nilsrenner/Selfe-Tuned-Filter/005_Dokumentation/003_Thesis/Theorie/bsb_einfacher_mulitplizierer.tex

%\documentclass[tikz,border=10pt]{standalone}
%\usepackage{tikz}
%\usetikzlibrary{arrows.meta, positioning}

%\begin{document}

\begin{tikzpicture}
    [  wcircle/.style={draw, fill=white, circle, minimum size=2.5em, inner sep=0pt},
       lcircle/.style={draw, fill=white, circle, minimum size= 0.5em, inner sep=0pt},
       connector/.style={-Latex, thick},
       node distance=2cm and 2cm]

\node[lcircle] (input1) {};
\node[wcircle, right=of input1] (gain) {$\prod$};
\node[lcircle, below=of gain] (input2) {};
\node[lcircle, right=of gain] (output) {};

\draw[connector] (input1) -- (gain) node[near start,above] {$V_x$};
\draw[connector] (input2) -- (gain) node[near start, left] {$V_y$};
\draw[connector] (gain) -- (output) node[near end, above] {$V_{out}$};
    
\end{tikzpicture}

%\end{document}
