nilsrenner/Selfe-Tuned-Filter/005_Dokumentation/Vorbereitung/report/docs/index.html

# Vorbereitung Bachlorarbeit

Autor:in

Zugehörigkeit

Nils Renner

Hochschule Bremen - City University of Applied Sciences (HSB) (https://www.hs-bremen.de)

Veröffentlichungsdatum

20. September 2025

Andere Formate

PDF

Zusammenfassung

Lorem ipsum

# 1 Einleitung

Durch das Modul ANS im letzten Semester wurde das arbeiten mit klassischen Analogen Filtern durch das Experiment 4 aus dem ASLK-Manual erlernt

Durch Berechnungen und Ausprobieren wurden analoge Filter entworfen und an die gewollten werte angepasst.

So ergaben sich Filter mit fester Freqenz, da die Bauteilgrößen einmal angenommen wurden (mit ausnahme der zwei Potis) und sich daraus die Frequenz ergab

In Experiment 5 des ASLK-Manuals soll es um selfe tuned Filter, also sich selbst automatisch anpassende/einstellende Filter gehen.

## 1.1 Motivation

In der Praxis schanken Bauteile (Temperatur, Alterung, Toleranzen).

Diese Probleme haben Filter die sich selbst einstellen nicht, da sie nicht rein von den physischen Paramentern der eingebauten Bauteile abhängen sondern einen gewissen Spielraum bieten, diese Inperfektionen auszugleichen.

Ziel ist es, dass der Filter selbstständig seine Mittenfrequenz nachstimmen kann. Dafür braucht er eine Referenzfrequenz und einen Mechanismus, der Prüft, ob der Filter noch auf der richtigen Frequenz liegt, oder weggedriftet ist.

Vorgehen: lernen wie man einen geregelten osz verwendet um Ref-Frequenz zu erzeugen. Ref-Frequenz wird verwendet um filter automaisch auf die Sollfrequenz einzustellen. Experiment ist also eine Kombination aus REgelungstechnik und Exp 4 (klassische Filtertheorie)

\[ V_o=V_{offset}+K_x \cdot V_x + K_y \cdot V_y + K_o \cdot V_x \cdot V_y \cdot \xi \tag{1}\]

Tolle Formel: Gleichung 1

# 2 Filter-Entwurf

# 3 Charakterisierung

# Literaturverzeichnis
