nilsrenner/Selfe-Tuned-Filter/005_Dokumentation/003_Thesis/Auswertung/Auswertung.pdf

# Kapitel 1

# Auswertung

In diesem Kapitel werden die Ergebnisse der Endmessungen präsentiert und analysiert. Da die zweite Platineniteration erst zwei Wochen vor der Abgabe eintraf, beziehen sich alle nachfolgenden Messwerte auf die Version 1 des pcb.

Die vorgestellten Ergebnisse basieren somit auf der erste Iteration, welche mit einer Versorgungsspannung von ±11 V betrieben wird. Die resultierende Referenzspannung der Multiplizierer beträgt dabei anstatt der angestrebten 10 V nur etwa 9,74 V. Die Ergebnisse der zweiten Platineniteration werden im Rahmen der Verteidigung vorgestellt.

## 1.1 Kleinsingnalanalyse des Gesamtsystems

Die Kleinsignalanalyse über den Red Pitaya liefert auch nach der Optimierung der einzelnen Bauteile des Systems keine neuen Ergebnisse. Der bisher ungeklährte Verlauf bleibt konsistent und ist in Abbildung 1.2 dargestellt.

1

Nils Renner (5197659) | Vorbereitung Bachelorthesis

../Bilder/mess_ac_final.png

Abbildung 1.1: ac-Final

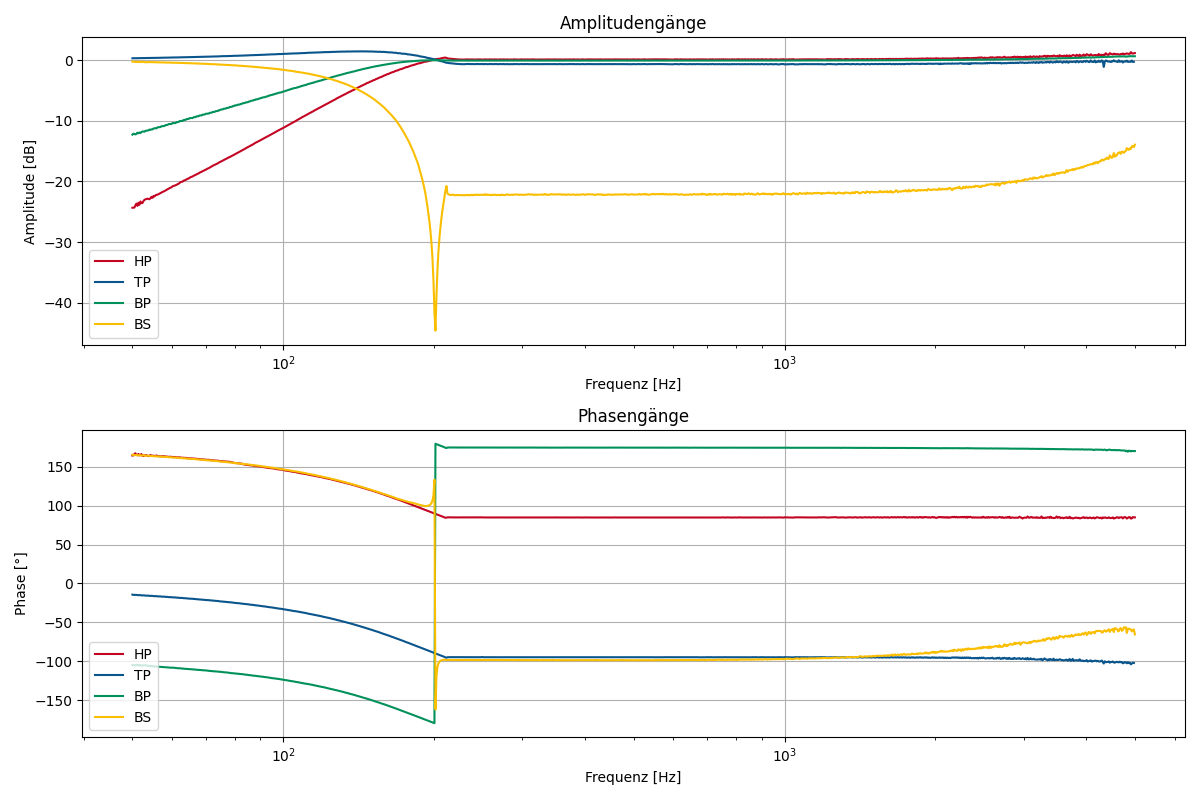
[picture p164: figure]

Abbildung 1.2: ac-Final

Wie bereits in Kapitel ?? erläutert, stagnieren die Amplituden- und Phasenverläufe kurz nach Erreichen der Resonanzfrequenz. Eine Vermutung für dieses Verhalten hängt mit der Arbeitsweise des Self-Tuned Filters zusammen, der versucht seine Resonanzfrequenz immer auf die eingehende Frequenz einzustellen.

Wird nun ein in der Frequenz kontinuierlich steigendes Eingangssignal angelegt, stellt sich der Filter erst in Richtung der geringen Startfrequenz ein. In Abbldung 1.2 ist bei etwa 200 Hz zu sehen, wie Resonanzfrequenz und Eingangsfrequenz übereinstimmen. Anschließend versucht der Fitler der steigenden Eingangsfrequenz zu folgen, bleibt aber aufgrund der gerineren Änderungsrate hinter der Eingangsfrequenz zurück. In diesem Fall wäre die Kleinsignalanalyse nicht zur Charakterisierung des Filters geeignet.

Um diese Hypothese zu überprüfen, wird die Anzahl der Messpunkte von 100 auf 1000 erhöht. Die höhere Anzahl führt zu einer langsameren Veränderung der Eingangsspannung, da der Red Pitaya die Frequenzpunkte nacheinander abarbeitet und jeder eine bestimmte Aufnahmezeit benötigt. Die dabei aufgenommenen Ergebnisse zeigen keine Veränderung zu vorherigen Messungen. Das Problem besteht also nicht in der zu geringen Änderungsrate des Systems.

Das genaue Verhalten des Systems bei der Kleinsignalanalyse kann durch diese alleinige Beobachtung also nicht genau geklärt werden.
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
