nilsrenner/Selfe-Tuned-Filter/005_Dokumentation/003_Thesis/Messung/Messung.pdf

# Kapitel 1

# Aufnahme der Messergebnisse

Bevor die ersten Messungen am System gemacht werden können, muss diese ausreichend auf ihre Funktionsfähigkeit getestet werden. Aufgrund der langen Lieferzeit der bestellten Bauteile gab es im Vorfeld ausreichend Zeit ein kleines Testprotokoll zu erarbeiten.

## 1.1 Funktionstest der Leiterplatte

Nach Fertigstellung des pcb wird zunächst der aufkommende Versorgungsstrom auf einen definierten Wert begrenzt. Anschließend wird kontrolliert, ob der Buck-Converter die 3,3 V zuverlässig ausgibt. Sobald das funktioniert, kann die Ansteuerung der Digitalpotentiometer durch die mcu programmiert werden. Mithilfe der zuvor geplanten Jumper kann der daraus resultierende Widerstandswert unabhängig von der Restschaltung gemessen und der Code dadurch validiert werden.
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
