nilsrenner/Selfe-Tuned-Filter/001_Analoge_Schaltungen/bilder/bp_160.png

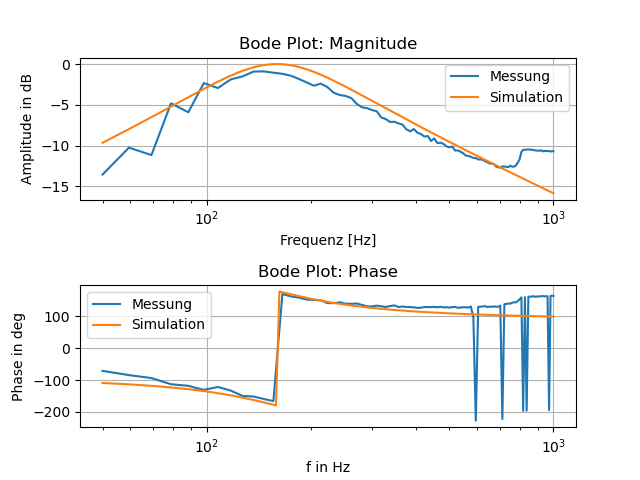
001_Analoge_Schaltungen/bilder/bp_160.png
