nilsrenner/Selfe-Tuned-Filter/001_Analoge_Schaltungen/bilder/hp_160_vgl.png

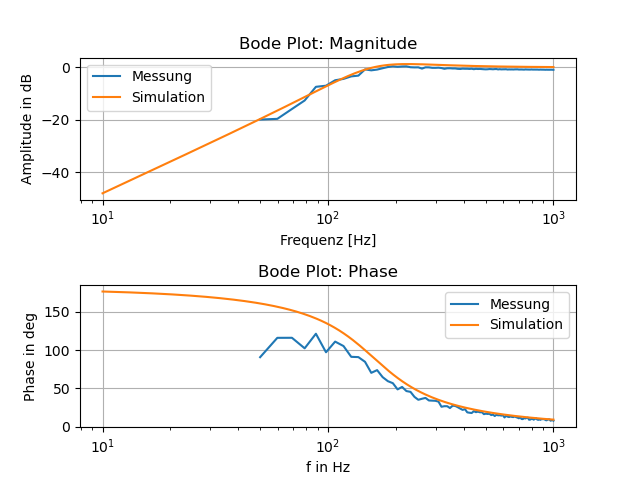
001_Analoge_Schaltungen/bilder/hp_160_vgl.png
