nilsrenner/Selfe-Tuned-Filter/001_Analoge_Schaltungen/bilder/lp_160.png

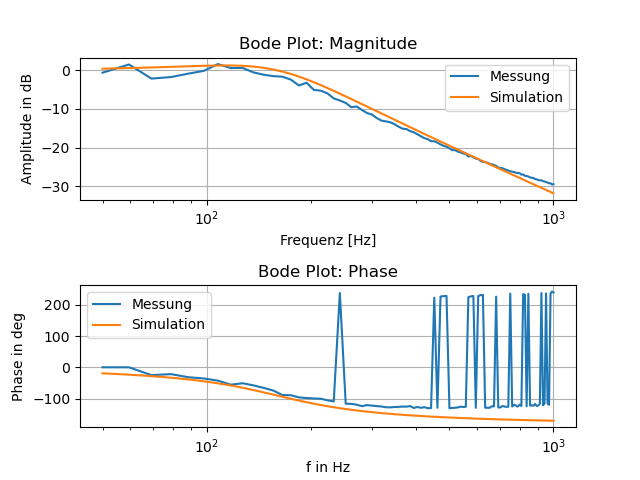
001_Analoge_Schaltungen/bilder/lp_160.png
