nilsrenner/Selfe-Tuned-Filter/001_Analoge_Schaltungen/bilder/lp_160_vgl.png

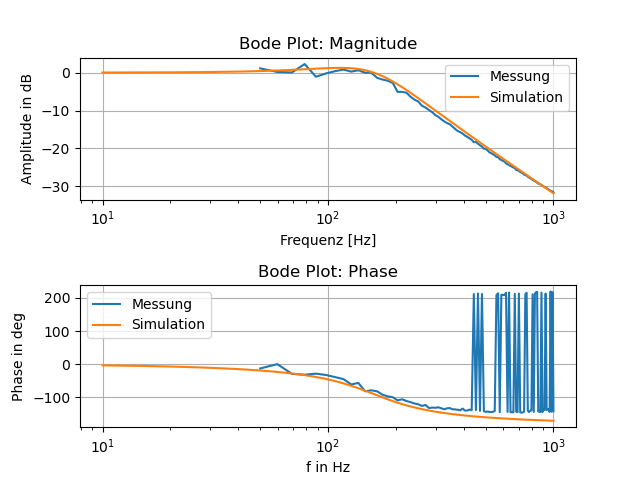
001_Analoge_Schaltungen/bilder/lp_160_vgl.png
