nilsrenner/Selfe-Tuned-Filter/001_Analoge_Schaltungen/Chap4/freq_sweep_bp_Q1.jpg

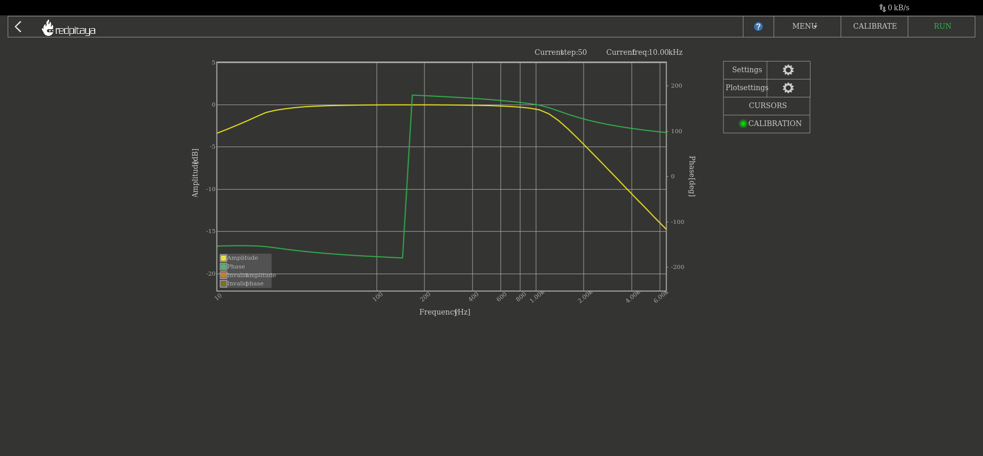
001_Analoge_Schaltungen/Chap4/freq_sweep_bp_Q1.jpg
