nilsrenner/Selfe-Tuned-Filter/001_Analoge_Schaltungen/Chap4/freq_sweep_bs_Q1.jpg

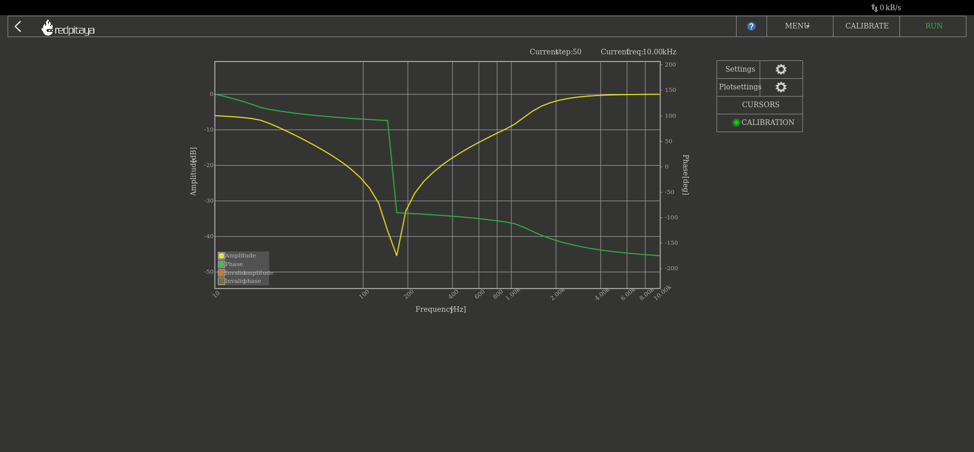
001_Analoge_Schaltungen/Chap4/freq_sweep_bs_Q1.jpg
