nilsrenner/Selfe-Tuned-Filter/003_Messdaten/004_Phase_Detector/SCR01.PNG

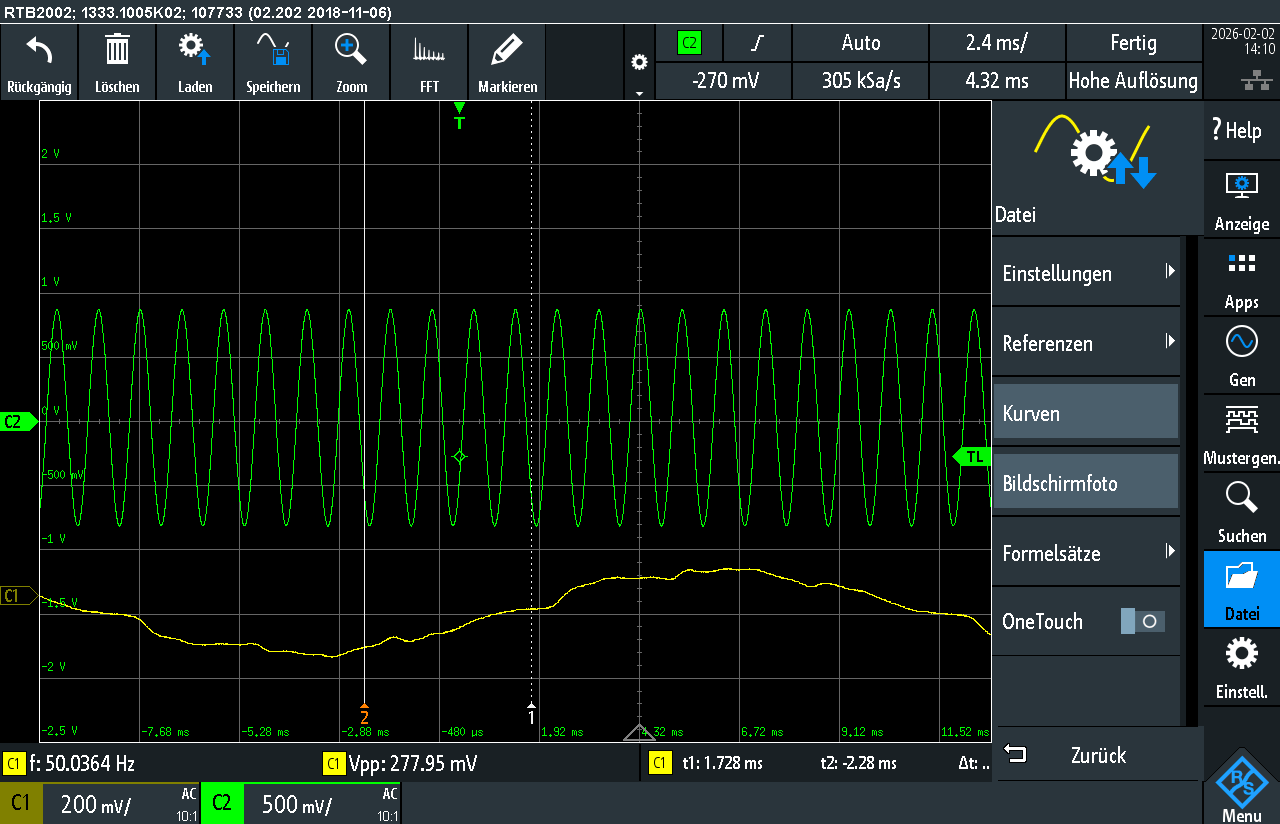
003_Messdaten/004_Phase_Detector/SCR01.PNG
