nilsrenner/Selfe-Tuned-Filter/003_Messdaten/004_Phase_Detector/SCR03.PNG

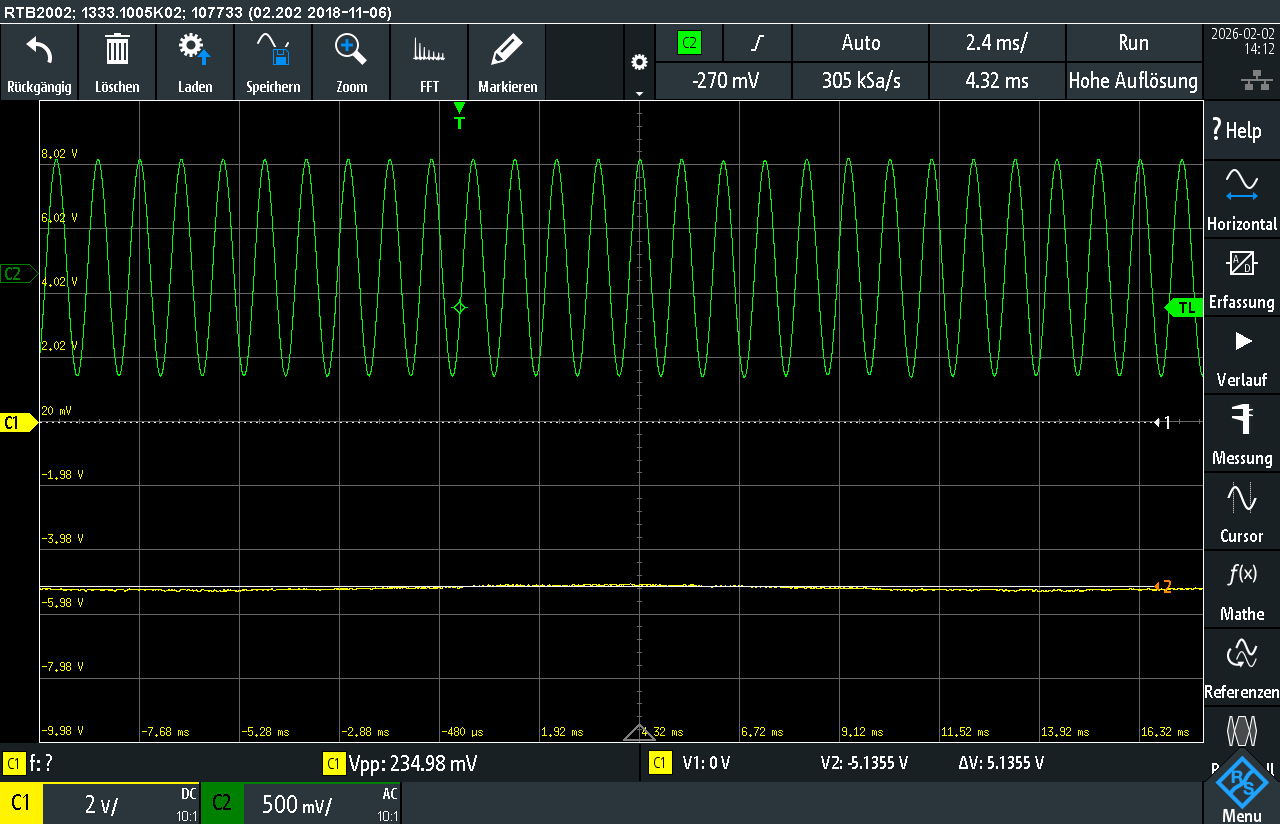
003_Messdaten/004_Phase_Detector/SCR03.PNG
