nilsrenner/Selfe-Tuned-Filter/003_Messdaten/004_Phase_Detector/SCR04.PNG

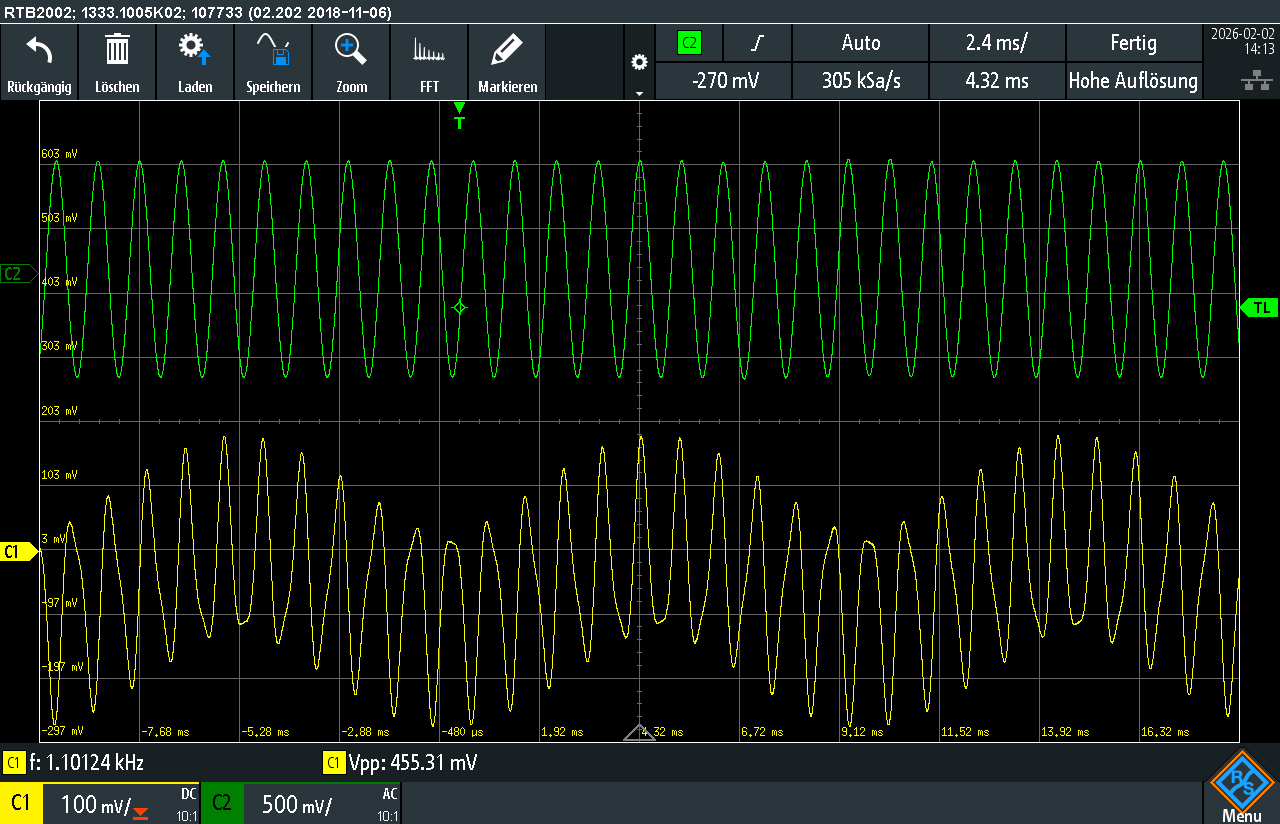
003_Messdaten/004_Phase_Detector/SCR04.PNG
