nilsrenner/Selfe-Tuned-Filter/003_Messdaten/004_Phase_Detector/SCR09.PNG

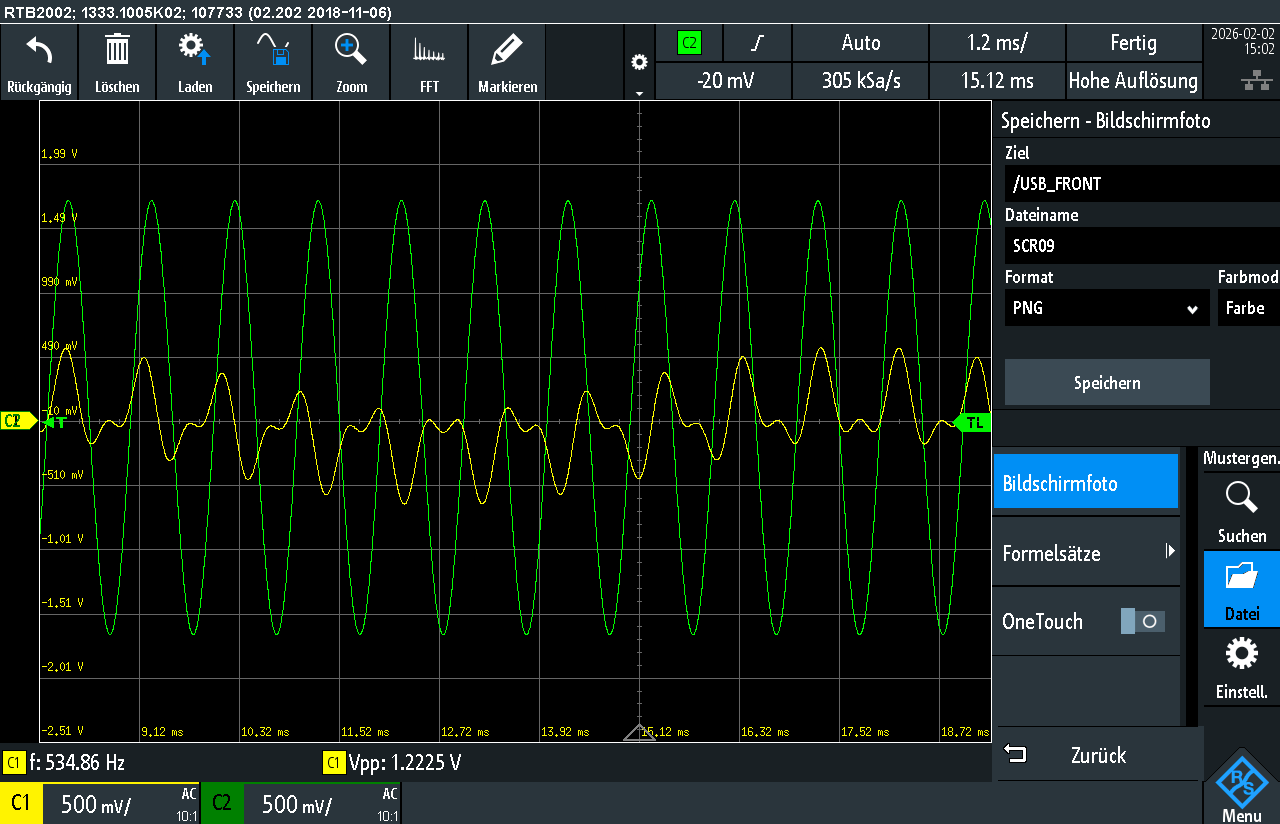
003_Messdaten/004_Phase_Detector/SCR09.PNG
