nilsrenner/Selfe-Tuned-Filter/003_Messdaten/004_Phase_Detector/SCR11.PNG

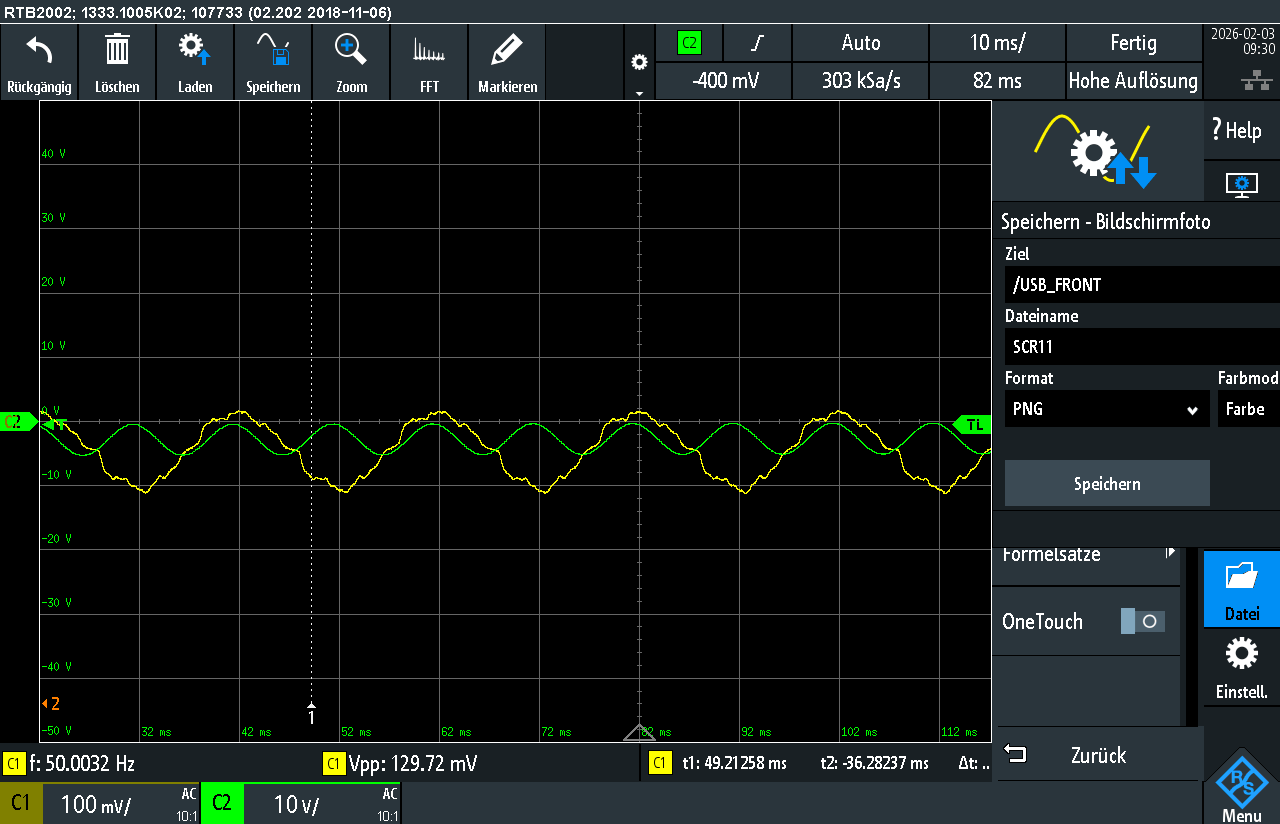
003_Messdaten/004_Phase_Detector/SCR11.PNG
