nilsrenner/Selfe-Tuned-Filter/003_Messdaten/004_Phase_Detector/SCR12.PNG

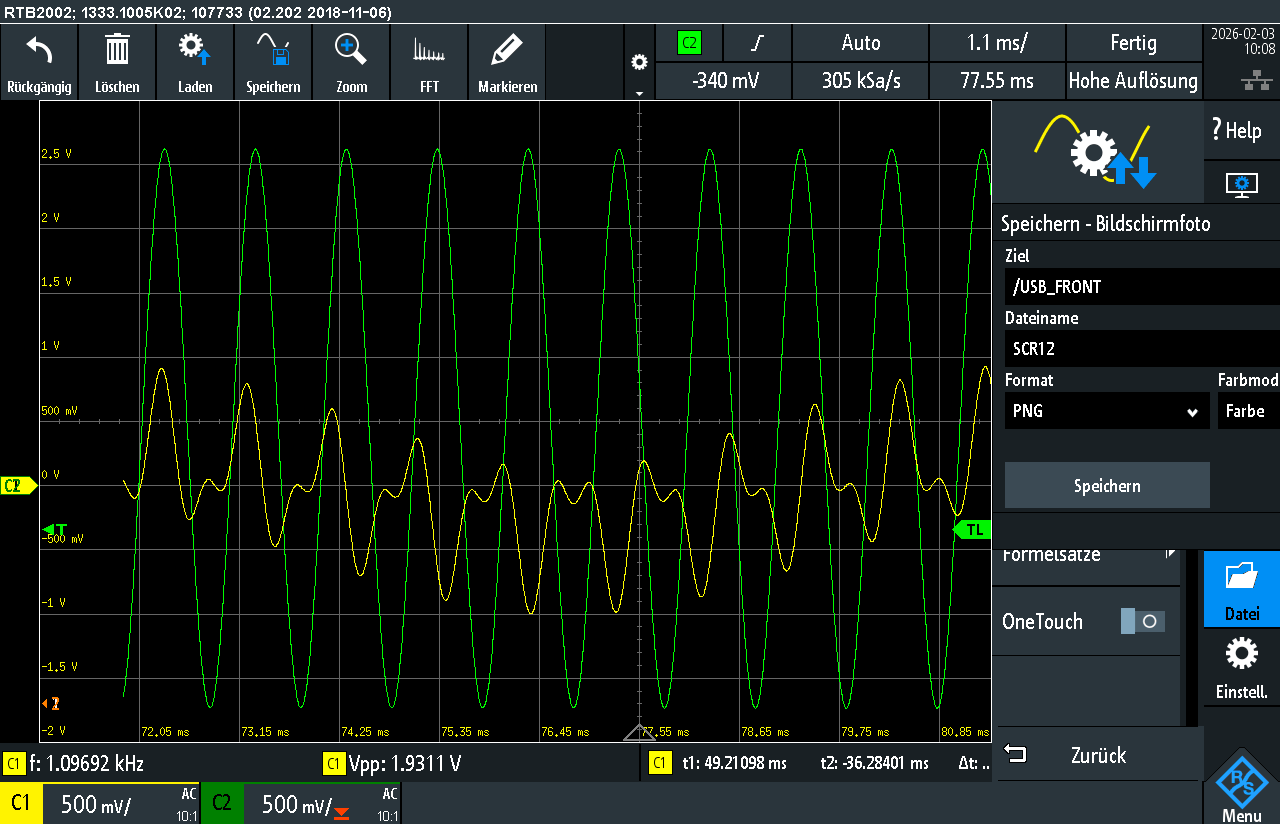
003_Messdaten/004_Phase_Detector/SCR12.PNG
