nilsrenner/Selfe-Tuned-Filter/003_Messdaten/amplitude_phase_plots.png

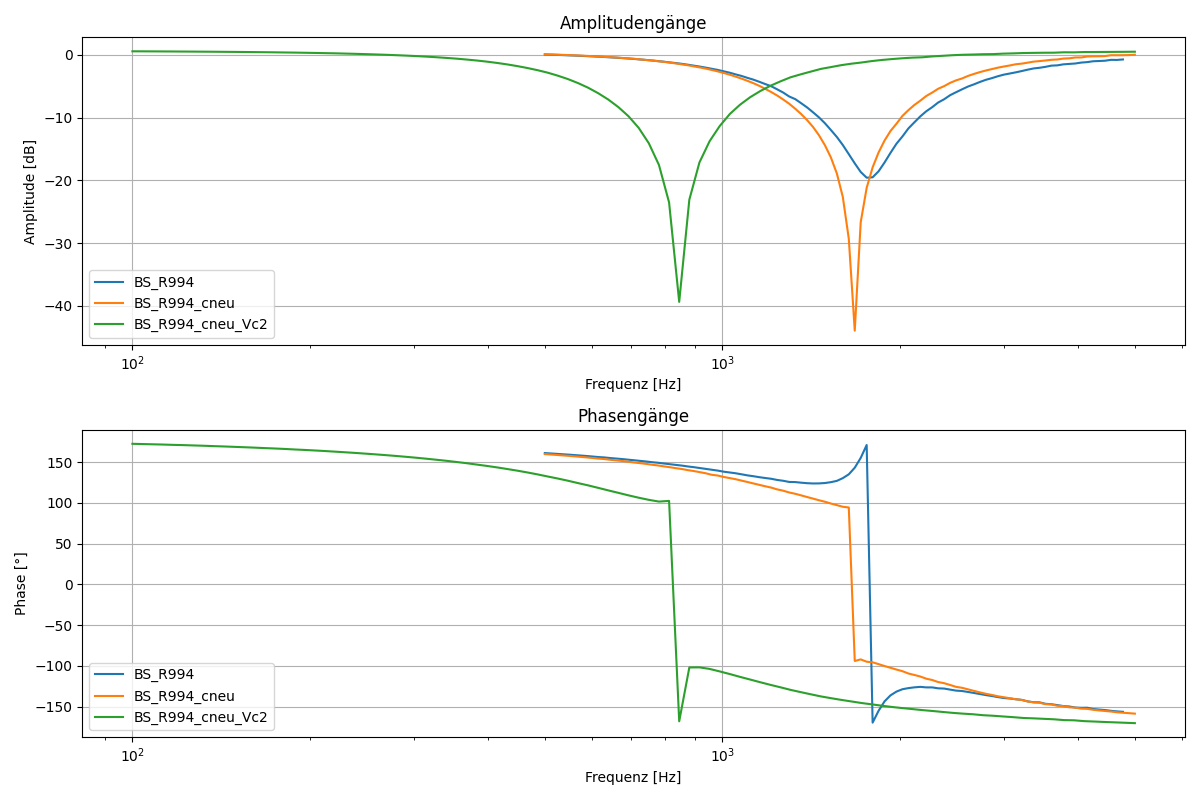
003_Messdaten/amplitude_phase_plots.png
