nilsrenner/Selfe-Tuned-Filter/005_Dokumentation/003_Thesis/Bilder/Messung_ges_sys_ac.png

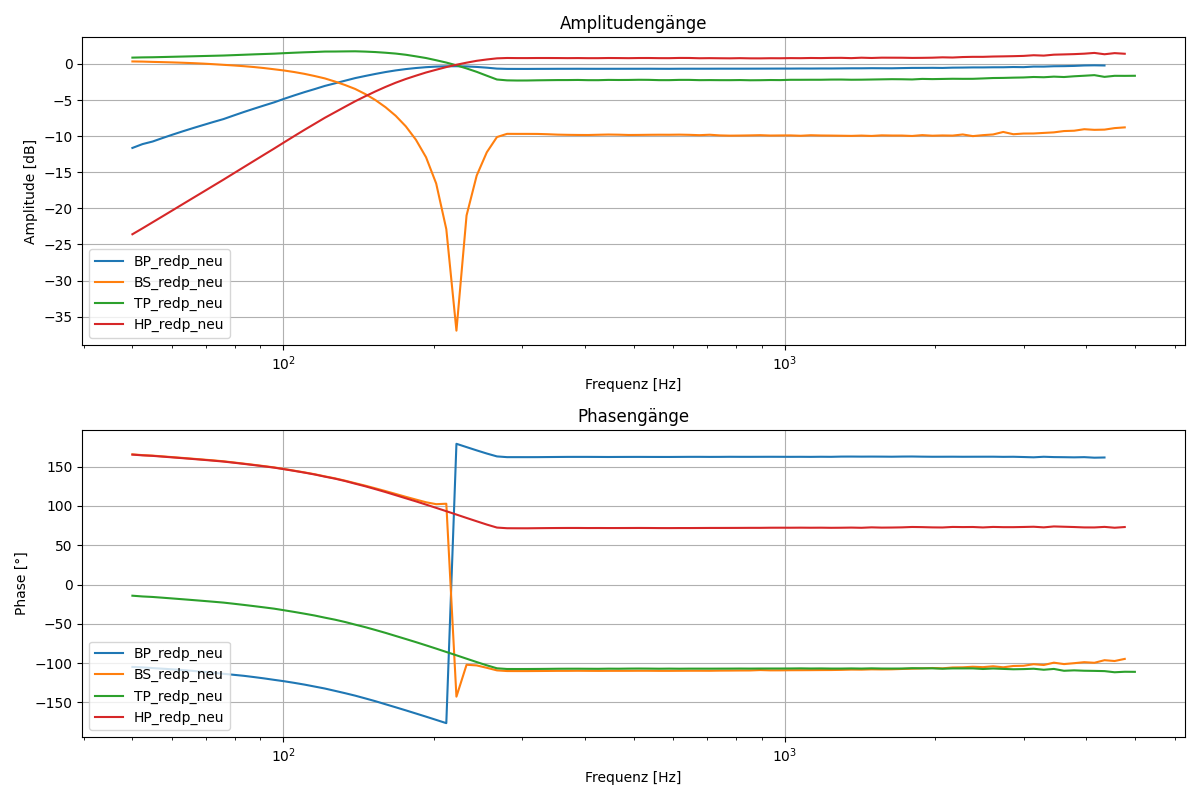
005_Dokumentation/003_Thesis/Bilder/Messung_ges_sys_ac.png
