nilsrenner/Selfe-Tuned-Filter/005_Dokumentation/003_Thesis/Bilder/pd_out_osc2.png

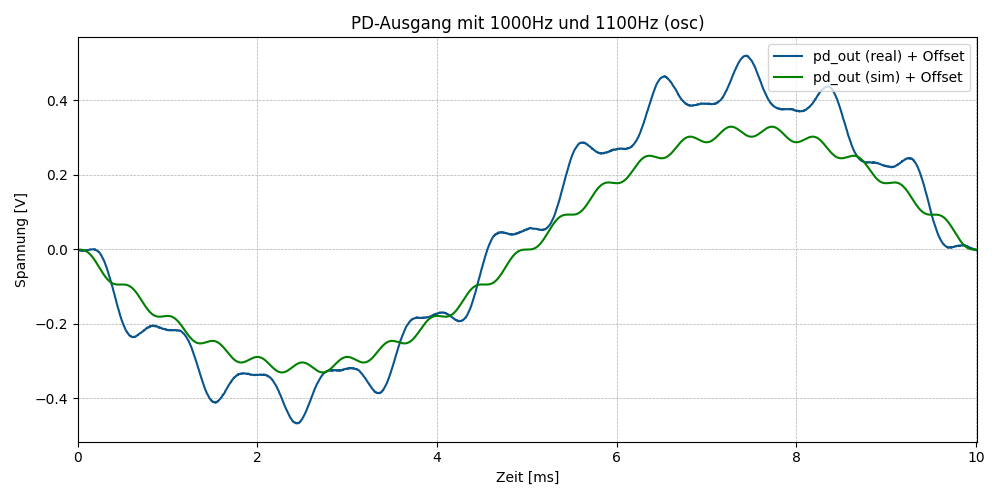
005_Dokumentation/003_Thesis/Bilder/pd_out_osc2.png
