nilsrenner/Selfe-Tuned-Filter/005_Dokumentation/003_Thesis/Bilder/ramp_vgl.png

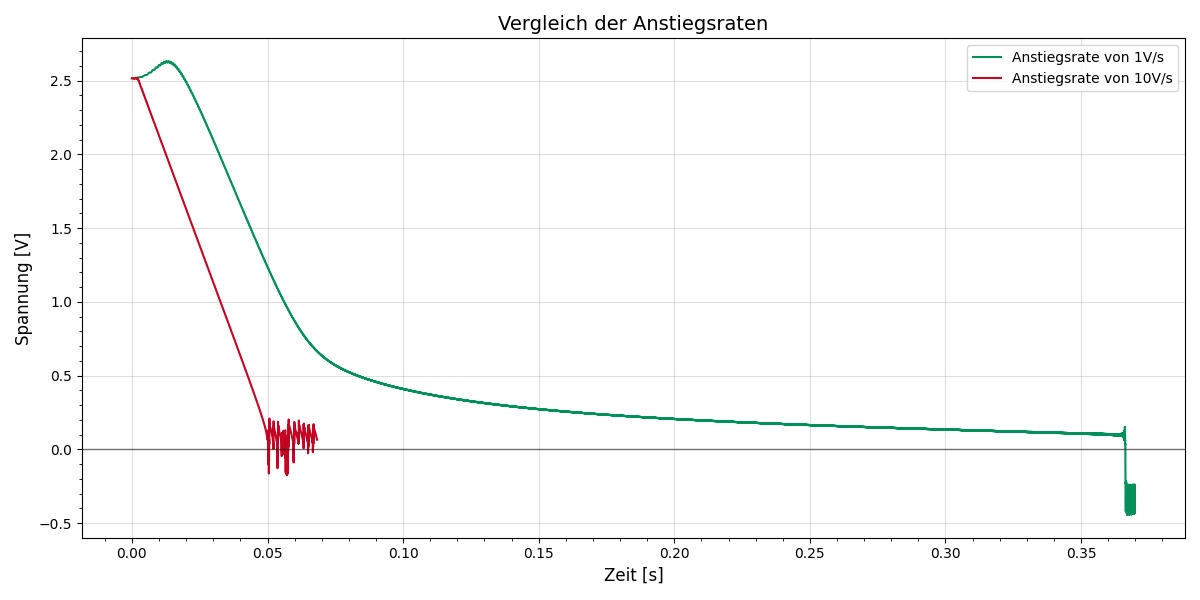
005_Dokumentation/003_Thesis/Bilder/ramp_vgl.png
