nilsrenner/Selfe-Tuned-Filter/005_Dokumentation/003_Thesis/Bilder/sim_fallhöhe.png

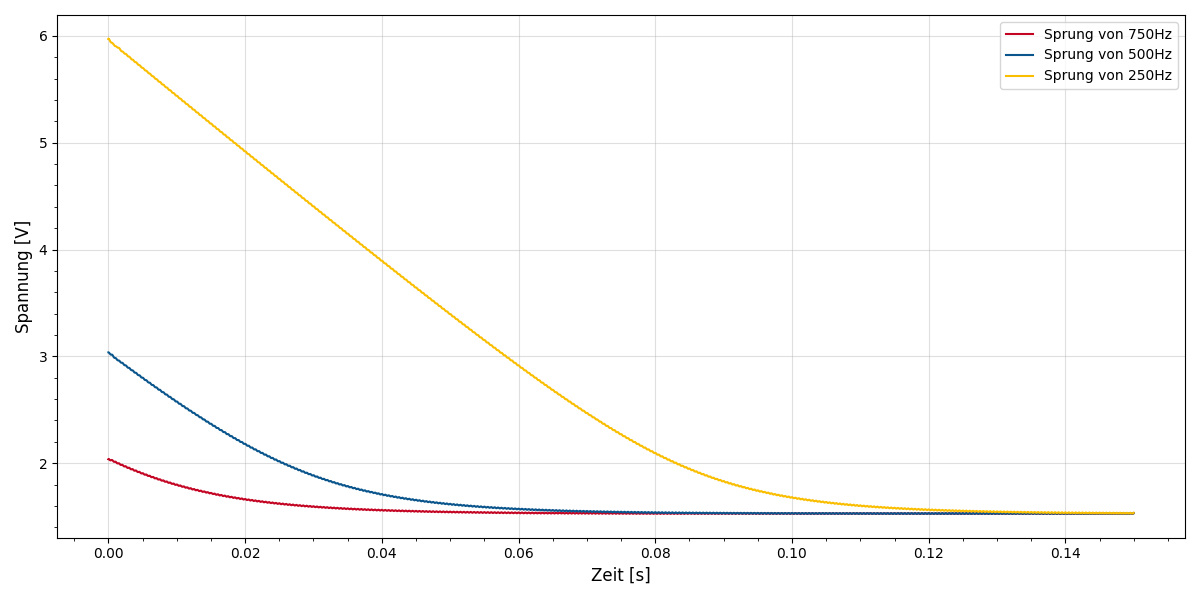
005_Dokumentation/003_Thesis/Bilder/sim_fallhöhe.png
