nilsrenner/Selfe-Tuned-Filter/005_Dokumentation/003_Thesis/Bilder/sprung_BP_BS.png

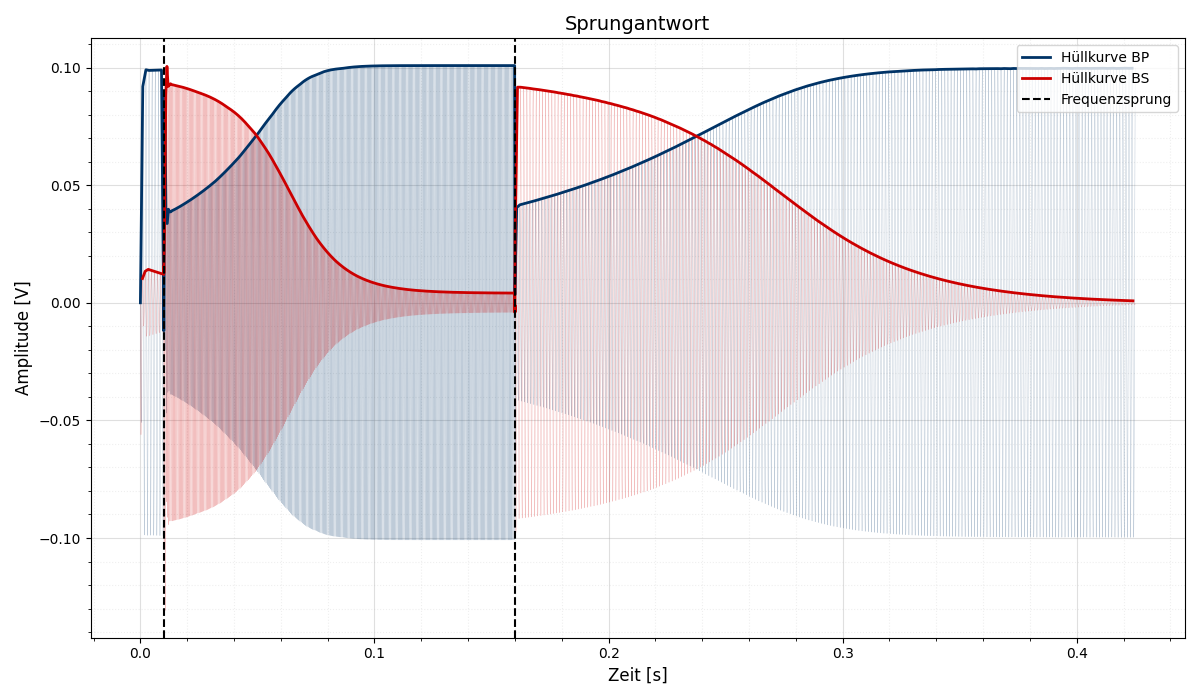
005_Dokumentation/003_Thesis/Bilder/sprung_BP_BS.png
