nilsrenner/Selfe-Tuned-Filter/005_Dokumentation/003_Thesis/Bilder/sprung_HP_TP.png

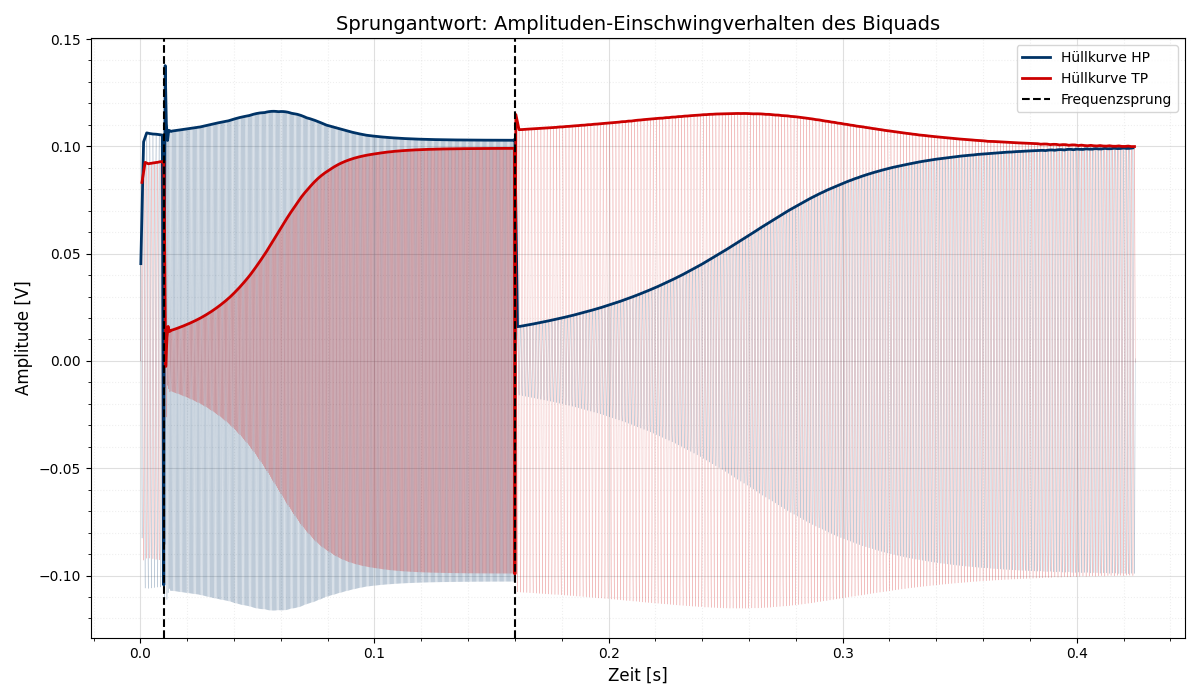
005_Dokumentation/003_Thesis/Bilder/sprung_HP_TP.png
