nilsrenner/Selfe-Tuned-Filter/005_Dokumentation/003_Thesis/Bilder/sprung_int_pd_out.png

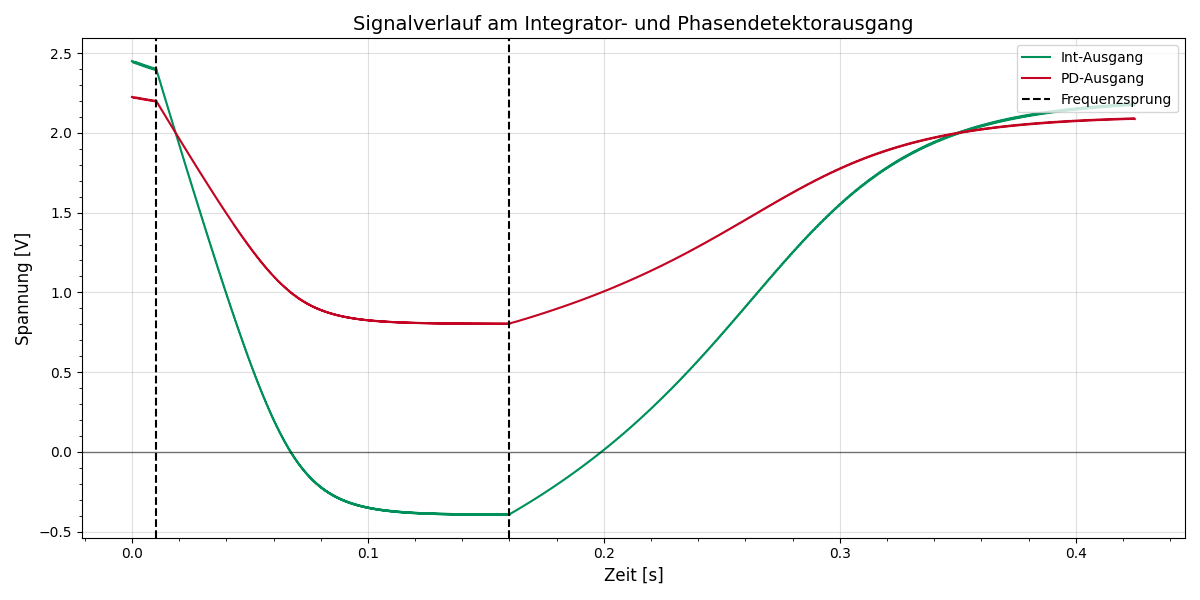
005_Dokumentation/003_Thesis/Bilder/sprung_int_pd_out.png
