nilsrenner/Selfe-Tuned-Filter/005_Dokumentation/003_Thesis/Bilder/sprung_knick_pd_out.png

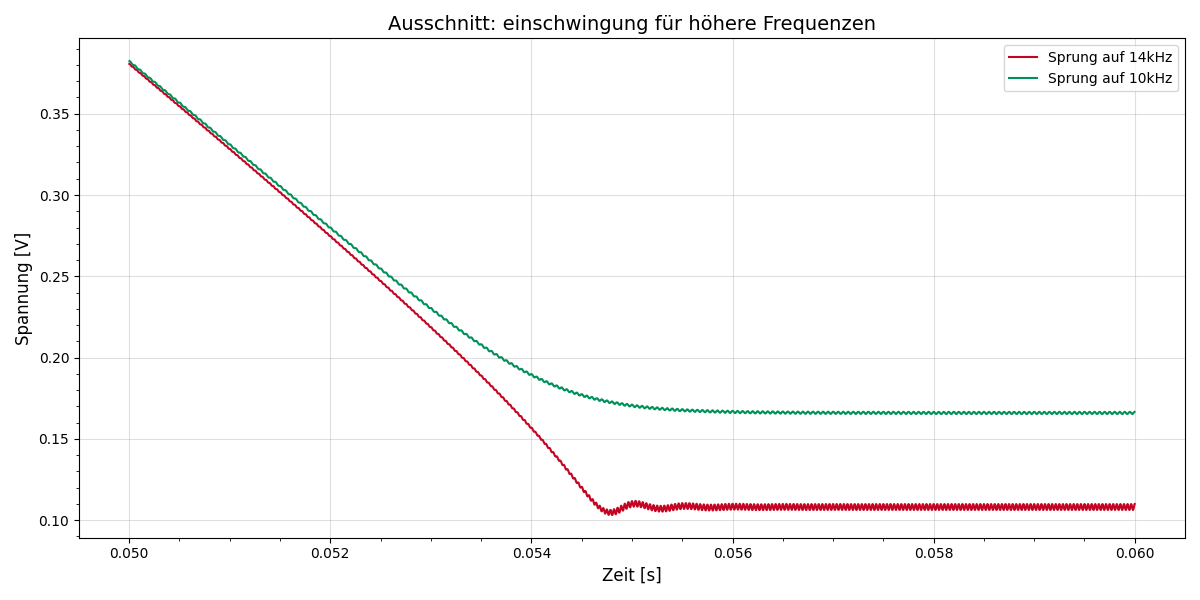
005_Dokumentation/003_Thesis/Bilder/sprung_knick_pd_out.png
