nilsrenner/Selfe-Tuned-Filter/005_Dokumentation/003_Thesis/Bilder/sprung_mess_vc.png

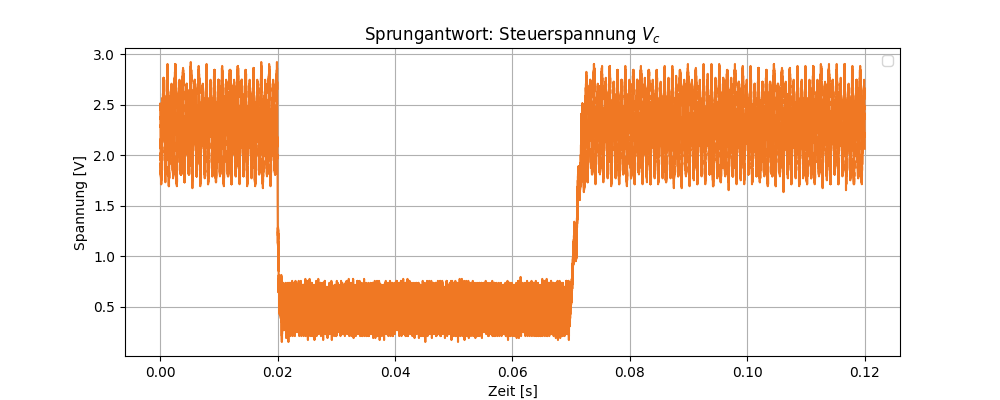
005_Dokumentation/003_Thesis/Bilder/sprung_mess_vc.png
