nilsrenner/Selfe-Tuned-Filter/005_Dokumentation/003_Thesis/Bilder/sprung_pd_out_diff_r.png

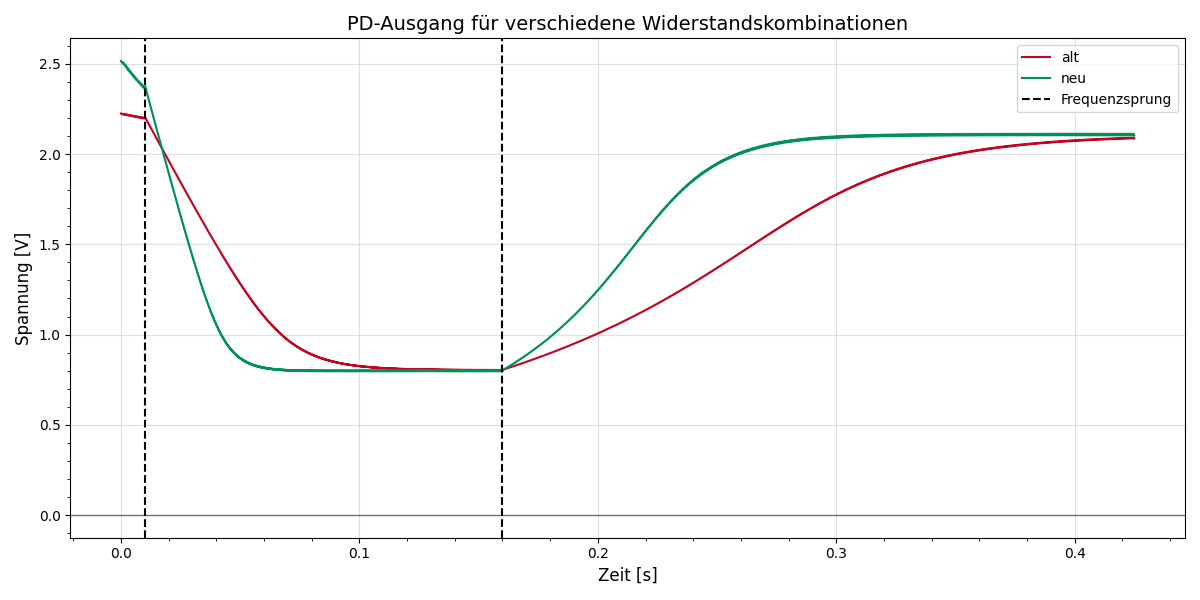
005_Dokumentation/003_Thesis/Bilder/sprung_pd_out_diff_r.png
