nilsrenner/Selfe-Tuned-Filter/001_Analoge_Schaltungen/bilder/Test_BS1.png

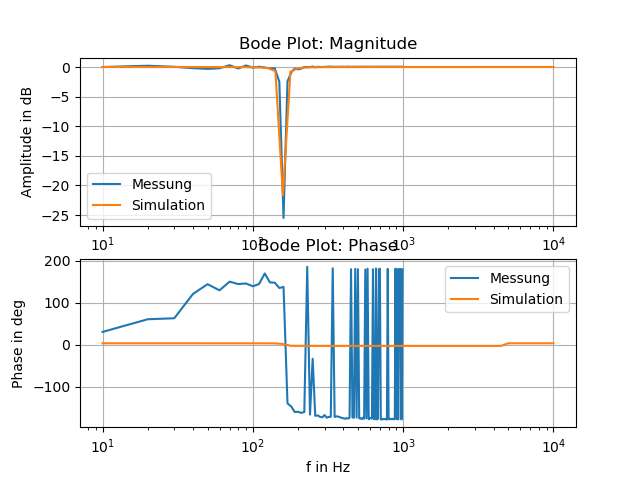
001_Analoge_Schaltungen/bilder/Test_BS1.png
