nilsrenner/Selfe-Tuned-Filter/001_Simulation_und_Schaltungsentwurf/008_LTSpice/spice_tran_tune_bereich.asc

B1: bv; V=0.1*sin(2*pi*(100+19900*V(f_pulse))*time)
C1: cap; 1µ
C2: cap; 1µ
C3: cap; 100n
R1: res; 1k
R2: res; 1k
R3: res; 1k
R4: res; 1k
R5: res; 1k
R6: res; 1k
R7: res; 1k
R8: res; 1k
R9: res; 100
R10: res; 100
R11: res; 100k
U9: mpy634
U10: opamp2; tl082
U11: opamp2; tl082
U12: opamp2; tl082
U13: opamp2; tl082
U14: opamp2; tl082
U15: mpy634
U16: mpy634
V1: voltage; 2
V2: voltage; PULSE(0 1 0 1 0 0 0)
V_OP1: voltage; 11
V_OP2: voltage; 11
VE1: voltage; 9.74
Named nets: 0, V_r, V+, V-, Mult3_out, Mult2_out, Mult1_out, V_F3, V_HP, V_Int, V_F2, V_TP, V_F1, V_in, f_pulse
.tran 425m
.inc tl082.cir
.inc mpy634_tina.lib
