nilsrenner/Selfe-Tuned-Filter/001_Simulation_und_Schaltungsentwurf/008_LTSpice/spice_tune_bereich.asc

B1: bv; V=0.1*sin(2*pi*(100+19900*V(f_ctrl))*time)
C1: cap; 1µ
C2: cap; 1µ
C3: cap; 100n
R1: res; 1k
R2: res; 1k
R3: res; 1k
R4: res; 100
R5: res; 1k
R6: res; 1k
R7: res; 1k
R8: res; 1k
R9: res; 1k
R10: res; 100
R11: res; 100k
U1: opamp2; tl082
U2: opamp2; tl082
U3: opamp2; tl082
U4: opamp2; tl082
U5: opamp2; tl082
U6: mpy634
U7: mpy634
U8: mpy634
V3: voltage; 2
V_ctrl: voltage; PULSE(0 10 0 1 0 0 0)
V_OP+: voltage; 11
V_OP-: voltage; 11
VDD1: voltage; 11
VE1: voltage; 10
VSS1: voltage; 11
Named nets: 0, V+, V-, vdd, vss, ve, V_F1, V_F2, V_TP, V_HP, V_F3, f_ctrl
*.ac dec 1000 50 5000
.inc tl082.cir
.inc mpy634.cir
.tran 0 500 0
*;step param R_C list 1k 25k 100k
.param C=1u Cx3=1u R=1k R_C=1k
*;dc V3 0 5 0.1
*;ac dec 50 50 1000
