nilsrenner/Selfe-Tuned-Filter/001_Simulation_und_Schaltungsentwurf/008_LTSpice/Experiment_05_Julian.asc

C1: cap; 1µ
C2: cap; 1µ
C3: cap; 1µ
R1: res; 993
R2: res; 990
R3: res; 1k
R4: res; 1k
R5: res; 1k
R6: res; 1k
R7: res; 990
R8: res; 984
R9: res; 1k
R10: res; 1k
R11: res; 1k
U1: opamp2; tl082
U2: opamp2; tl082
U3: opamp2; tl082
U4: opamp2; tl082
U5: opamp2; tl082
U6: mpy634
U7: mpy634
U8: mpy634
V3: voltage; 2
V_OP+: voltage; 11
V_OP-: voltage; 11
VDD1: voltage; 11
VE1: voltage; 9.74
VG1: voltage; SINE(0 100m 2k 0 0 0); AC 1 0
VSS1: voltage; 11
Named nets: 0, V+, V-, vdd, vss, ve, V_F1, V_F2, V_TP, V_HP, V_F3
*.ac dec 1000 50 5000
.inc tl082.cir
.inc mpy634.cir
.tran 10m
*;step param R_C list 1k 25k 100k
.param C=1u Cx3=1u R=1k R_C=1k
*;dc V3 0 5 0.1
*;ac dec 50 50 1000
