nilsrenner/Selfe-Tuned-Filter/001_Analoge_Schaltungen/schaltungsentwurf_no1/schaltungsentwurf_no1.kicad_sch

## KiCad design 001_Analoge_Schaltungen/schaltungsentwurf_no1/schaltungsentwurf_no1.kicad_sch (2025-09-09)

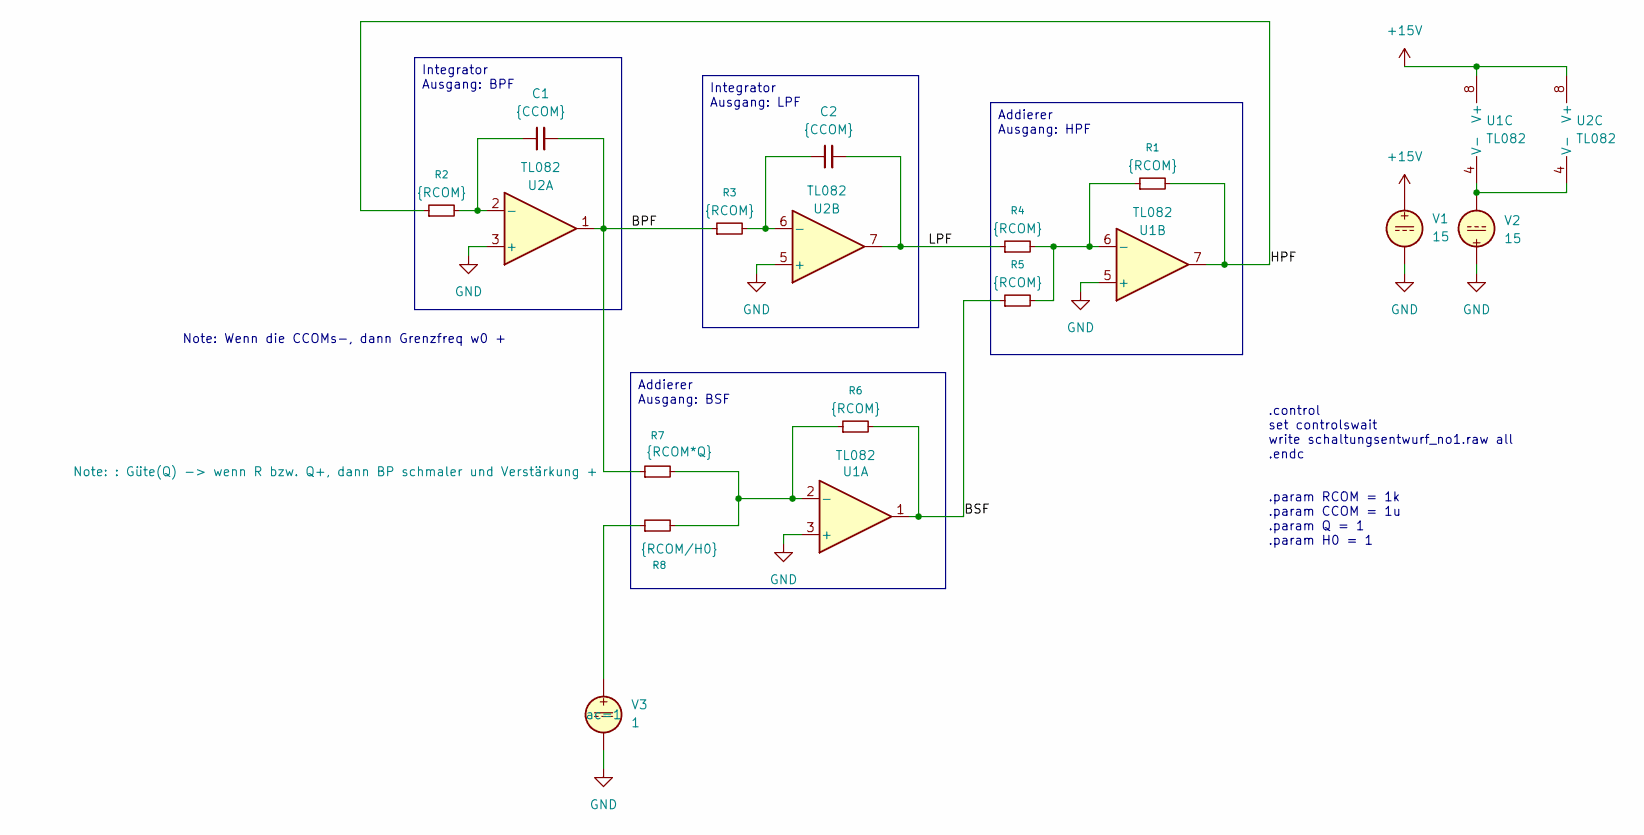
[picture p224: schematic schaltungsentwurf_no1.kicad_sch]

Parts:
C1, C2: {CCOM}
R1, R2, R3, R4, R5, R6: {RCOM}; Resistor
R7: {RCOM*Q}; Trimmer straight
R8: {RCOM/H0}; Trimmer straight
U1, U2: TL082; CERDIP-8_W7.62mm_SideBrazed_LongPads_Socket
V1, V2: 15
V3: 1

Connections:
+15V: U1.8 (V+), U2.8 (V+), V1.1
BPF: C1.2, R3.1, R7.1, U2.1
BSF: R5.1, R6.2, U1.1
GND: U1.3 (+), U1.5 (+), U2.3 (+), U2.5 (+), V1.2, V2.1, V3.2
HPF: R1.2, R2.1, U1.7
LPF: C2.2, R4.1, U2.7
unnamed: C1.1, R2.2, U2.2 (-)
unnamed: C2.1, R3.2, U2.6 (-)
unnamed: R1.1, R4.2, R5.2, U1.6 (-)
unnamed: R6.1, R7.2, R8.2, U1.2 (-)
unnamed: R8.1, V3.1
unnamed: U1.4 (V-), U2.4 (V-), V2.2

Notes on the sheet:
.control set controlswait write schaltungsentwurf_no1.raw all .endc
Note: Wenn die CCOMs-, dann Grenzfreq w0 +
.param RCOM = 1k .param CCOM = 1u .param Q = 1 .param H0 = 1
Integrator Ausgang: LPF
Addierer Ausgang: HPF
Addierer Ausgang: BSF
Integrator Ausgang: BPF
